AtmatiAdi/JoDo/sr_szablon_projekt/figures/20200416_172317.jpg

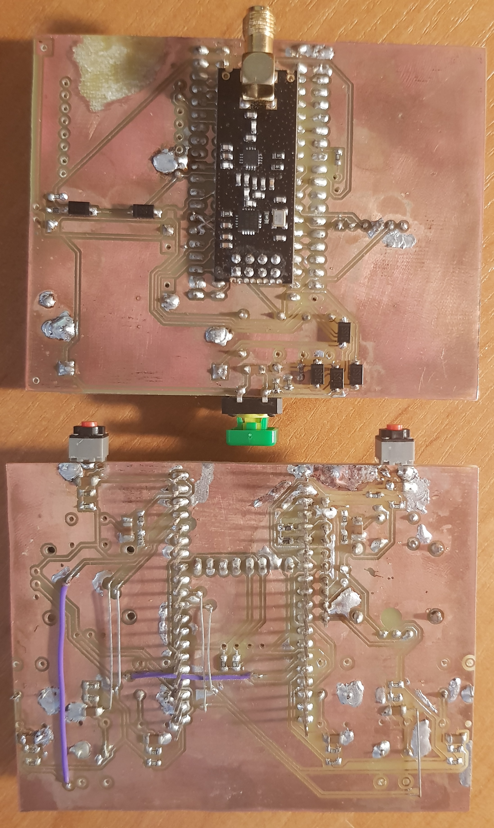
sr_szablon_projekt/figures/20200416_172317.jpg
