AtmatiAdi/JoDo/sr_szablon_projekt/figures/20200416_172346.jpg

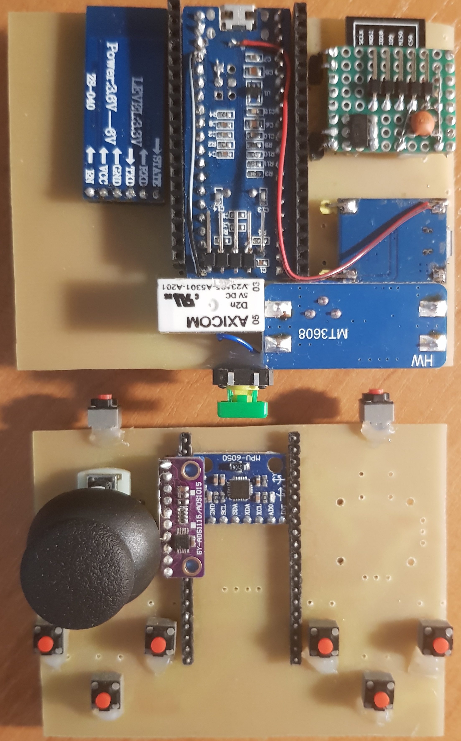
sr_szablon_projekt/figures/20200416_172346.jpg
