AtmatiAdi/JoDo/sr_szablon_projekt/figures/calosc2.jpg

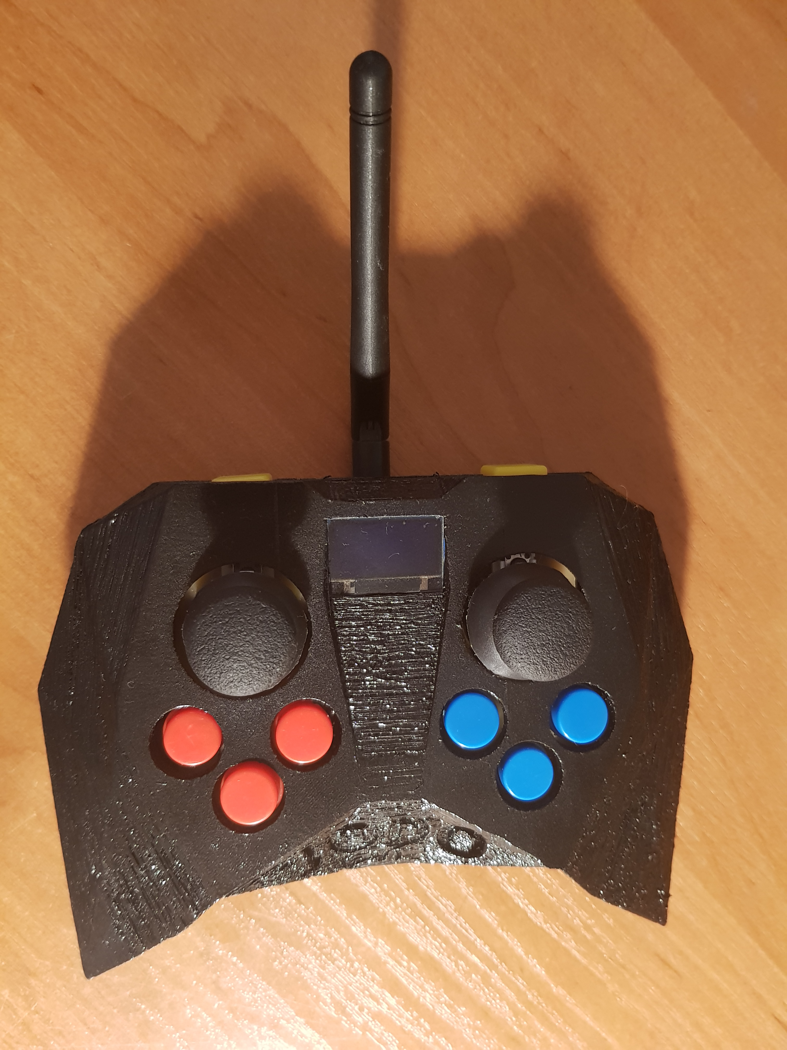
sr_szablon_projekt/figures/calosc2.jpg
