AtmatiAdi/JoDo/sr_szablon_projekt/figures/clock.PNG

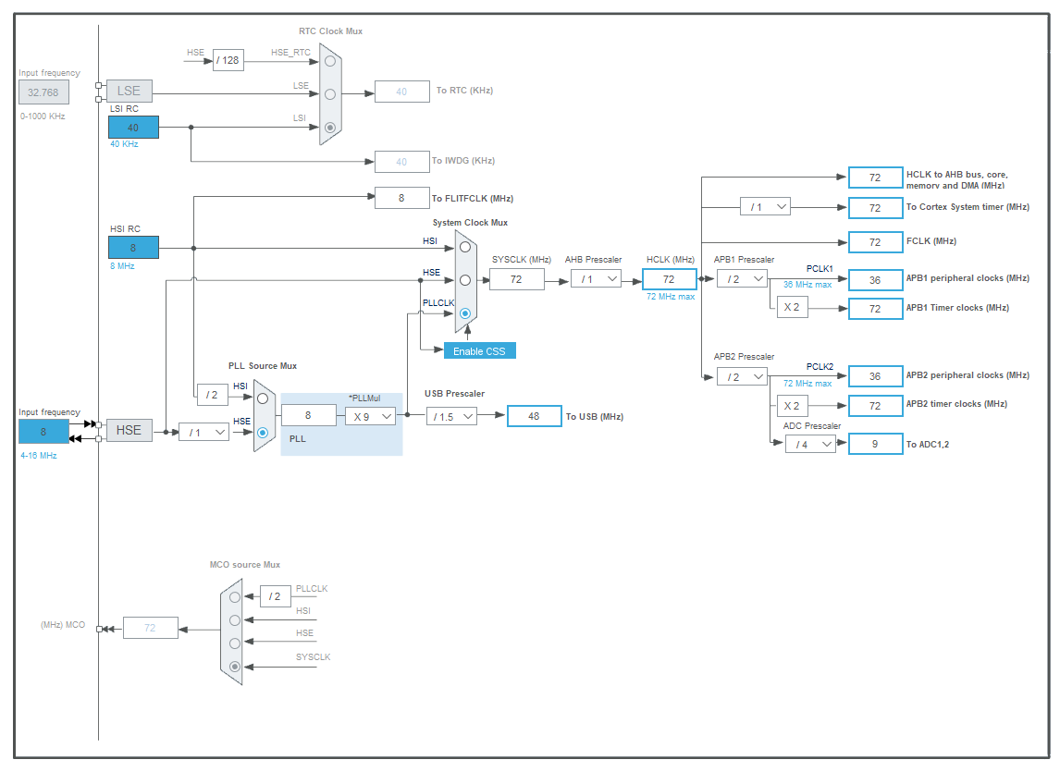
sr_szablon_projekt/figures/clock.PNG
