AtmatiAdi/JoDo/sr_szablon_projekt/figures/pcb_bot.PNG

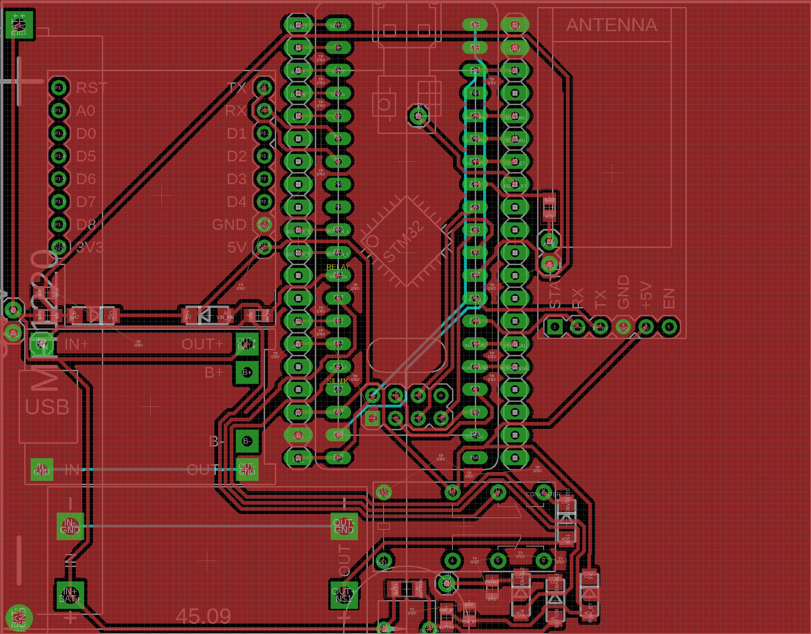
sr_szablon_projekt/figures/pcb_bot.PNG
