AtmatiAdi/JoDo/sr_szablon_projekt/figures/Przechwytywanie.PNG

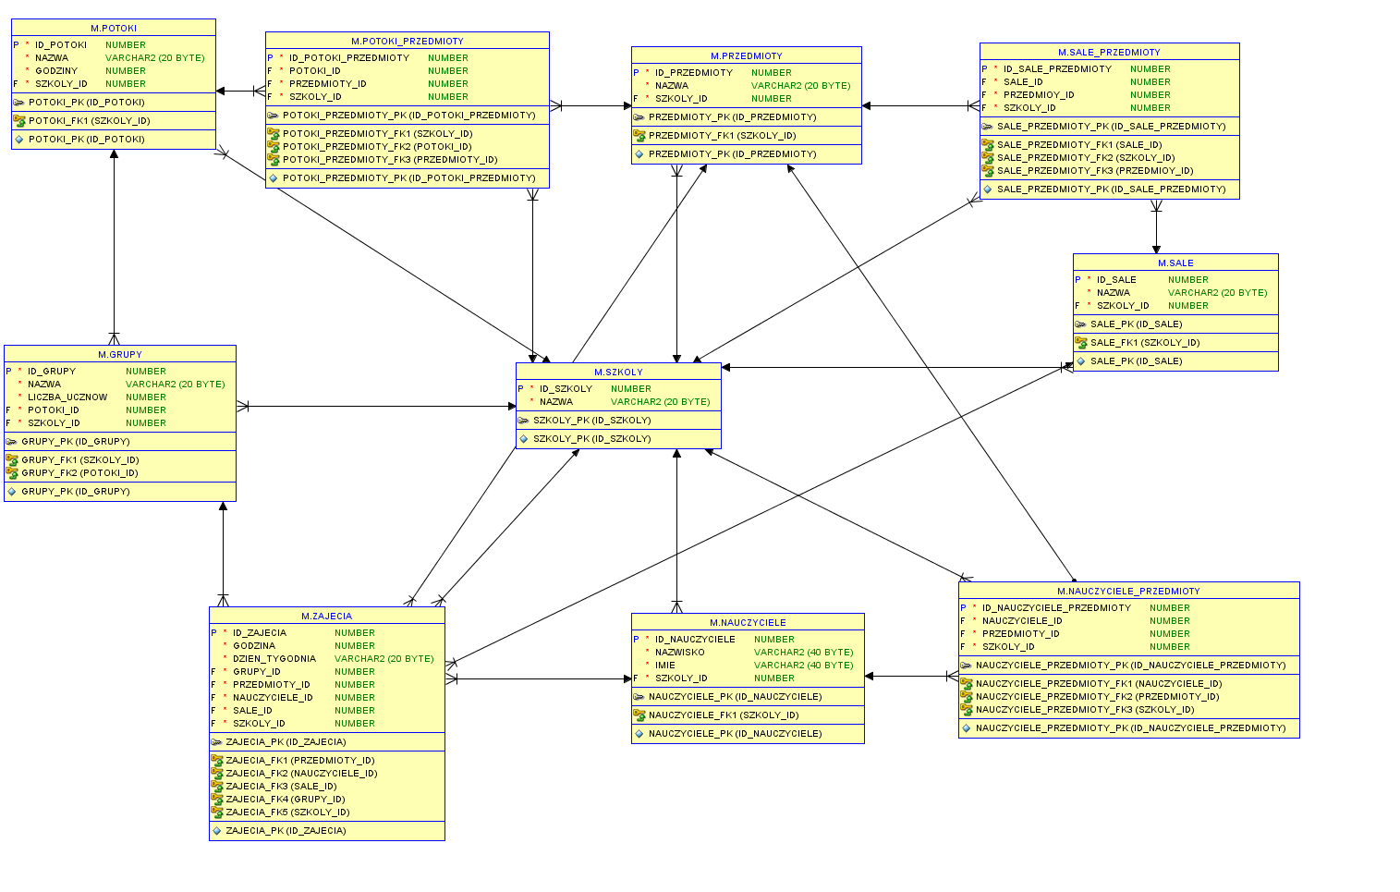
sr_szablon_projekt/figures/Przechwytywanie.PNG
