AtmatiAdi/JoDo/sr_szablon_projekt/figures/rep.PNG

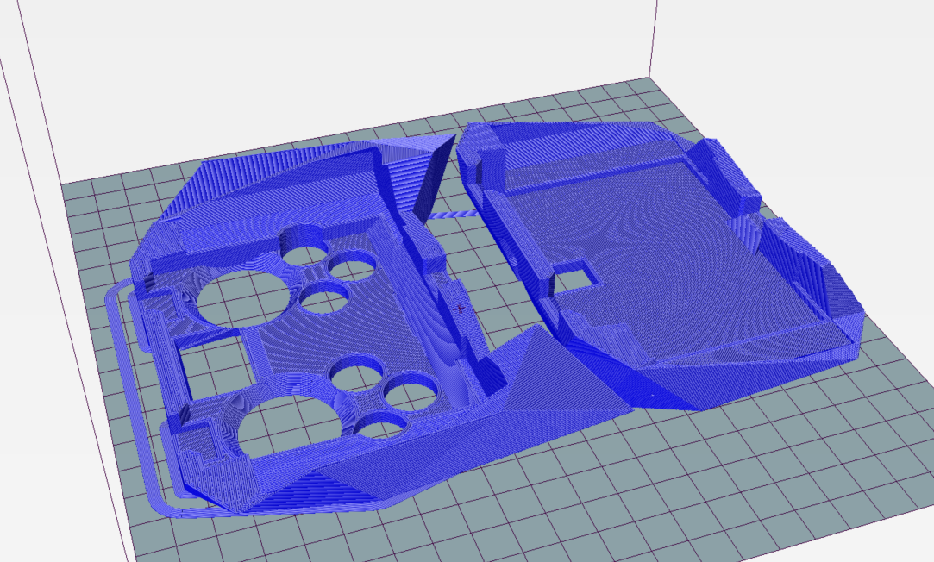
sr_szablon_projekt/figures/rep.PNG
