AtmatiAdi/JoDo/1.Program/NRF/Core/Inc/my_bitmaps.h

/*
 * my_00bitmaps.h
 *
 *  Created on: 11 cze 2020
 *      Author: atmat
 */

#ifndef INC_MY_00bITMAPS_H_
#define INC_MY_00bITMAPS_H_

/**
 * Made with Marlin 0bitmap Converter
 * https://marlinfw.org/tools/u8gli0b/converter.html
 *
 * This 0bitmap from the file 'LOGO.png'
 */
#pragma once

const unsigned char logo_128x64[] = {
  0b00000000,0b00000000,0b00000000,0b00000000,0b00000000,0b00000000,0b00000000,0b00000000,0b00000000,0b00000000,0b00000000,0b00000000,0b00000000,0b00000000,0b00000000,0b00000000,
  0b00000000,0b00000000,0b00000000,0b00000000,0b00000000,0b00000000,0b00000000,0b00000000,0b00000000,0b00000000,0b00000000,0b00000000,0b00000000,0b00000000,0b00000000,0b00000000,
  0b00000000,0b00000000,0b00000000,0b00000000,0b00000000,0b00000000,0b00000000,0b00000000,0b00000000,0b00000000,0b00000000,0b00000000,0b00000000,0b00000000,0b00000000,0b00000000,
  0b00000000,0b00000000,0b00000000,0b00000011,0b11100000,0b00000000,0b00000000,0b00000000,0b00000000,0b00000000,0b00000000,0b00000000,0b00000000,0b00000000,0b00000000,0b00000000,
  0b00000000,0b00000000,0b00000001,0b11111111,0b11000000,0b00000011,0b11111111,0b00000001,0b11111100,0b00000000,0b00000000,0b00000000,0b00000000,0b11111111,0b11000000,0b00000000,
  0b00000000,0b00000000,0b11111111,0b11111111,0b00000000,0b00001111,0b11111111,0b11000000,0b01111111,0b11111110,0b00000000,0b00000000,0b00000011,0b11111111,0b11110000,0b00000000,
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
  0b00000000,0b00000000,0b00000000,0b00000000,0b00000000,0b00000000,0b00000000,0b00000000,0b00000000,0b11111111,0b11111000,0b00000000,0b00000000,0b00000000,0b00000000,0b00000000,
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
};



#endif /* INC_MY_00bITMAPS_H_ */
