AtmatiAdi/JoDo/1.Program/NRF/Core/Inc/my_icons.h

/*
 * my_icons.h
 *
 *  Created on: 11 cze 2020
 *      Author: atmat
 */

#ifndef INC_MY_ICONS_H_
#define INC_MY_ICONS_H_


unsigned char home_icon16x16[] =
{
	0b00000111, 0b11100000, //      ######
	0b00001111, 0b11110000, //     ########
	0b00011111, 0b11111000, //    ##########
	0b00111111, 0b11111100, //   ############
	0b01111111, 0b11111110, //  ##############
	0b11111111, 0b11111111, // ################
	0b11000000, 0b00000011, // ##            ##
	0b11000000, 0b00000011, // ##            ##
	0b11000000, 0b00000011, // ##            ##
	0b11001111, 0b11110011, // ##  ########  ##
	0b11001111, 0b11110011, // ##  ########  ##
	0b11001100, 0b00110011, // ##  ##    ##  ##
	0b11001100, 0b00110011, // ##  ##    ##  ##
	0b11001100, 0b00110011, // ##  ##    ##  ##
	0b11111100, 0b00111111, // ######    ######
	0b11111100, 0b00111111, // ######    ######
};
 unsigned char arrow_up_icon16x16[] =
{
	0b00000001, 0b10000000, //        ##
	0b00000011, 0b11000000, //       ####
	0b00000111, 0b11100000, //      ######
	0b00001111, 0b11110000, //     ########
	0b00011110, 0b01111000, //    ####  ####
	0b00111100, 0b00111100, //   ####    ####
	0b01111000, 0b00011110, //  ####      ####
	0b11111100, 0b00111111, // ######    ######
	0b11111100, 0b00111111, // ######    ######
	0b01111100, 0b00111110, //  #####    #####
	0b00011100, 0b00111000, //    ###    ###
	0b00011100, 0b00111000, //    ###    ###
	0b00011100, 0b00111000, //    ###    ###
	0b00011111, 0b11111000, //    ##########
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
	0b00000000, 0b00000000, //
	0b00000000, 0b00000000, //
	0b00000000, 0b01000000, //          #
	0b00000000, 0b11000000, //         ##
	0b00000001, 0b11000000, //        ###
	0b00000001, 0b11000000, //        ###
	0b00000101, 0b11000000, //      # ###
	0b00001101, 0b11000000, //     ## ###
	0b00011101, 0b11000000, //    ### ###
	0b00011101, 0b11000000, //    ### ###
	0b01011101, 0b11000000, //  # ### ###
	0b11011101, 0b11000000, // ## ### ###
	0b11011101, 0b11000000, // ## ### ###
};
 unsigned char signal4_icon16x16[] =
{
	0b00000000, 0b00000000, //
	0b00000000, 0b00000100, //              #
	0b00000000, 0b00001100, //             ##
	0b00000000, 0b00011100, //            ###
	0b00000000, 0b00011100, //            ###
	0b00000000, 0b01011100, //          # ###
	0b00000000, 0b11011100, //         ## ###
	0b00000001, 0b11011100, //        ### ###
	0b00000001, 0b11011100, //        ### ###
	0b00000101, 0b11011100, //      # ### ###
	0b00001101, 0b11011100, //     ## ### ###
	0b00011101, 0b11011100, //    ### ### ###
	0b00011101, 0b11011100, //    ### ### ###
	0b01011101, 0b11011100, //  # ### ### ###
	0b11011101, 0b11011100, // ## ### ### ###
	0b11011101, 0b11011100, // ## ### ### ###
};
#endif /* INC_MY_ICONS_H_ */
