AtmatiAdi/JoDo/1.Program/NRF/Core/Src/my_usbd_custom_hid_if.c

/**
  ******************************************************************************
  * @file           : usbd_custom_hid_if.c
  * @brief          : USB Device Custom HID interface file.
  ******************************************************************************
  *
  * Copyright (c) 2017 STMicroelectronics International N.V. 
  * All rights reserved.
  *
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
  ******************************************************************************
*/

/* Includes ------------------------------------------------------------------*/
#include "my_usbd_custom_hid_if.h"
/** @addtogroup STM32_USB_OTG_DEVICE_LIBRARY
  * @{
  */

/** @defgroup USBD_CUSTOM_HID 
  * @brief usbd core module
  * @{
  */ 

/** @defgroup USBD_CUSTOM_HID_Private_TypesDefinitions
  * @{
  */ 
/**
  * @}
  */ 

/** @defgroup USBD_CUSTOM_HID_Private_Defines
  * @{
  */ 
  
/**
  * @}
  */ 

/** @defgroup USBD_CUSTOM_HID_Private_Macros
  * @{
  */ 
/**
  * @}
  */ 

/** @defgroup USBD_AUDIO_IF_Private_Variables
 * @{
 */
__ALIGN_BEGIN static uint8_t CUSTOM_HID_ReportDesc_FS[USBD_CUSTOM_HID_REPORT_DESC_SIZE] __ALIGN_END =
{
  /* USER CODE BEGIN 0 */ 
		0x06, 0x00, 0xff,              // USAGE_PAGE (Generic Desktop)
		    0x09, 0x01,                    // USAGE (Vendor Usage 1)
		    0xa1, 0x01,                    // COLLECTION (Application)
		    0x85, 0x01,                    //   REPORT_ID (1)
		    0x09, 0x01,                    //   USAGE (Vendor Usage 1)
		    0x15, 0x00,                    //   LOGICAL_MINIMUM (0)
		    0x25, 0x01,                    //   LOGICAL_MAXIMUM (1)
		    0x75, 0x08,                    //   REPORT_SIZE (8)
		    0x95, 0x01,                    //   REPORT_COUNT (1)
		    0xB1, 0x82,                    //   FEATURE (Data,Var,Abs,Vol)
		    0x85, 0x01,                    //   REPORT_ID (1)
		    0x09, 0x01,                    //   USAGE (Vendor Usage 1)
		    0x91, 0x82,                    //   OUTPUT (Data,Var,Abs,Vol)

		    0x85, 0x02,                    //   REPORT_ID (2)
		    0x09, 0x02,                    //   USAGE (Vendor Usage 2)
		    0x15, 0x00,                    //   LOGICAL_MINIMUM (0)
		    0x25, 0x01,                    //   LOGICAL_MAXIMUM (1)
		    0x75, 0x08,                    //   REPORT_SIZE (8)
		    0x95, 0x01,                    //   REPORT_COUNT (1)
		    0xB1, 0x82,                    //   FEATURE (Data,Var,Abs,Vol)
		    0x85, 0x02,                    //   REPORT_ID (2)
		    0x09, 0x02,                    //   USAGE (Vendor Usage 2)
		    0x91, 0x82,                    //   OUTPUT (Data,Var,Abs,Vol)

		    0x85, 0x03,                    //   REPORT_ID (3)
		    0x09, 0x03,                    //   USAGE (Vendor Usage 3)
		    0x15, 0x00,                    //   LOGICAL_MINIMUM (0)
		    0x25, 0x01,                                      //   LOGICAL_MAXIMUM (255)
		    0x75, 0x08,                    //   REPORT_SIZE (8)
		    0x95, 0x01,                    //   REPORT_COUNT (1)
		    0xB1, 0x82,                    //   FEATURE (Data,Var,Abs,Vol)
		    0x85, 0x03,                    //   REPORT_ID (3)
		    0x09, 0x03,                    //   USAGE (Vendor Usage 3)
		    0x91, 0x82,                    //   OUTPUT (Data,Var,Abs,Vol)

		    0x85, 0x04,                    //   REPORT_ID (4)
		    0x09, 0x04,                    //   USAGE (Vendor Usage 4)
		    0x15, 0x00,                    //   LOGICAL_MINIMUM (0)
		    0x25, 0x01,                                      //   LOGICAL_MAXIMUM (255)
		    0x75, 0x08,                    //   REPORT_SIZE (8)
		    0x95, 0x01,                    //   REPORT_COUNT (1)
		    0xB1, 0x82,                    //   FEATURE (Data,Var,Abs,Vol)
		    0x85, 0x04,                    //   REPORT_ID (4)
		    0x09, 0x04,                    //   USAGE (Vendor Usage 4)
		    0x91, 0x82,                    //   OUTPUT (Data,Var,Abs,Vol)

		    0x85, 0x05,                    //   REPORT_ID (5)
		    0x09, 0x05,                    //   USAGE (Vendor Usage 5)
		    0x75, 0x08,                    //   REPORT_SIZE (8)
		    0x95, 0x04,                    //   REPORT_COUNT (4)
		    0x81, 0x82,                    //   INPUT (Data,Var,Abs,Vol)

		    0x85, 0x06,                    //   REPORT_ID (6)
		    0x09, 0x06,                    //   USAGE (Vendor Usage 6)
		    0x75, 0x08,                    //   REPORT_SIZE (8)
		    0x95, 0x04,                    //   REPORT_COUNT (4)
		    0x81, 0x82,                    //   INPUT (Data,Var,Abs,Vol)
  /* USER CODE END 0 */ 
  0xC0    /*     END_COLLECTION	             */
   
}; 

/**
  * @}
  */ 
  
/** @defgroup USBD_CUSTOM_HID_IF_Exported_Variables
  * @{
  */ 
  extern USBD_HandleTypeDef hUsbDeviceFS;
/**
  * @}
  */ 
  
/** @defgroup USBD_CUSTOM_HID_Private_FunctionPrototypes
  * @{
  */
static int8_t CUSTOM_HID_Init_FS     (void);
static int8_t CUSTOM_HID_DeInit_FS   (void);
static int8_t CUSTOM_HID_OutEvent_FS (uint8_t event_idx, uint8_t state);
 

USBD_CUSTOM_HID_ItfTypeDef USBD_CustomHID_fops_FS = 
{
  CUSTOM_HID_ReportDesc_FS,
  CUSTOM_HID_Init_FS,
  CUSTOM_HID_DeInit_FS,
  CUSTOM_HID_OutEvent_FS,
};

/**
  * @brief  CUSTOM_HID_Init_FS
  *         Initializes the CUSTOM HID media low layer
  * @param  None
  * @retval Result of the operation: USBD_OK if all operations are OK else USBD_FAIL
  */
static int8_t CUSTOM_HID_Init_FS(void)
{ 
  /* USER CODE BEGIN 4 */ 
  return (0);
  /* USER CODE END 4 */ 
}

/**
  * @brief  CUSTOM_HID_DeInit_FS
  *         DeInitializes the CUSTOM HID media low layer
  * @param  None
  * @retval Result of the operation: USBD_OK if all operations are OK else USBD_FAIL
  */
static int8_t CUSTOM_HID_DeInit_FS(void)
{
  /* USER CODE BEGIN 5 */ 
  return (0);
  /* USER CODE END 5 */ 
}

/**
  * @brief  CUSTOM_HID_OutEvent_FS
  *         Manage the CUSTOM HID class events       
  * @param  event_idx: event index
  * @param  state: event state
  * @retval Result of the operation: USBD_OK if all operations are OK else USBD_FAIL
  */
static int8_t CUSTOM_HID_OutEvent_FS  (uint8_t event_idx, uint8_t state)
{ 
  /* USER CODE BEGIN 6 */ 
  return (0);
  /* USER CODE END 6 */ 
}

/* USER CODE BEGIN 7 */ 
/**
  * @brief  USBD_CUSTOM_HID_SendReport_FS
  *         Send the report to the Host       
  * @param  report: the report to be sent
  * @param  len: the report length
  * @retval Result of the operation: USBD_OK if all operations are OK else USBD_FAIL
  */
/*
int8_t USBD_CUSTOM_HID_SendReport_FS ( uint8_t *report,uint16_t len)
{
	  return USBD_CUSTOM_HID_SendReport(&hUsbDeviceFS, report, len);
}
*/
/* USER CODE END 7 */ 

/* USER CODE BEGIN PRIVATE_FUNCTIONS_IMPLEMENTATION */
/* USER CODE END PRIVATE_FUNCTIONS_IMPLEMENTATION */

/**
  * @}
  */ 

/**
  * @}
  */  
/************************ (C) COPYRIGHT STMicroelectronics *****END OF FILE****/
